Cranyozen/QF_HP_HWJRT/找羊量产初号机资料/贴纸/高壓危險.jpg

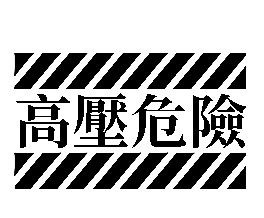
找羊量产初号机资料/贴纸/高壓危險.jpg
