Cranyozen/QF_HP_HWJRT/固件/ESP8266/include/bmp.h

#ifndef _BMP_H_
#define _BMP_H_

const unsigned char circle_shi[] = {
	9, 9, 0x38, 0xFE, 0xFE, 0xFF, 0xFF, 0xFF, 0xFE, 0xFE, 0x38, 0x00, 0x00, 0x00, 0x01, 0x01, 0x01, 0x00,
	0x00, 0x00, /*"E:\Program\通用库\图标库\图标库\实心选择圆.bmp",0*/
				/* (9 X 9 )*/

};

const unsigned char circle_kong[] = {
	9, 9, 0x38, 0xC6, 0x82, 0x01, 0x01, 0x01, 0x82, 0xC6, 0x38, 0x00, 0x00, 0x00, 0x01, 0x01, 0x01, 0x00,
	0x00, 0x00, /*"E:\Program\通用库\图标库\图标库\空心选择圆.bmp",0*/
				/* (9 X 9 )*/

};

const unsigned char number[10][80] = // 20*32
	{
		// 0
		{
			0xFF, 0xFF, 0xFF, 0x07, 0x07, 0x07, 0x07, 0x07, 0x07, 0x07, 0x07, 0x07, 0x07, 0x07, 0x07, 0x07,
			0x07, 0xFF, 0xFF, 0xFF, 0xFF, 0xFF, 0xFF, 0x00, 0x00, 0x00, 0x00, 0x00, 0x00, 0x00, 0x00, 0x00,
			0x00, 0x00, 0x00, 0x00, 0x00, 0xFF, 0xFF, 0xFF, 0xFF, 0xFF, 0xFF, 0x00, 0x00, 0x00, 0x00, 0x00,
			0x00, 0x00, 0x00, 0x00, 0x00, 0x00, 0x00, 0x00, 0x00, 0xFF, 0xFF, 0xFF, 0xFF, 0xFF, 0xFF, 0xE0,
			0xE0, 0xE0, 0xE0, 0xE0, 0xE0, 0xE0, 0xE0, 0xE0, 0xE0, 0xE0, 0xE0, 0xE0, 0xE0, 0xFF, 0xFF, 0xFF, // 0
		},

		// 1
		{
			0x00, 0x00, 0x70, 0x70, 0x38, 0x38, 0x1C, 0x1C, 0x0E, 0x0E, 0xFF, 0xFF, 0xFF, 0x00, 0x00, 0x00,
			0x00, 0x00, 0x00, 0x00, 0x00, 0x00, 0x00, 0x00, 0x00, 0x00, 0x00, 0x00, 0x00, 0x00, 0xFF, 0xFF,
			0xFF, 0x00, 0x00, 0x00, 0x00, 0x00, 0x00, 0x00, 0x00, 0x00, 0x00, 0x00, 0x00, 0x00, 0x00, 0x00,
			0x00, 0x00, 0xFF, 0xFF, 0xFF, 0x00, 0x00, 0x00, 0x00, 0x00, 0x00, 0x00, 0xE0, 0xE0, 0xE0, 0xE0,
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
	0x00, 0x01, 0x02, 0x04, 0x09, 0x12, 0x24, 0x48, 0x90, 0x20, 0x40, 0x80, 0x00, 0x00, 0x00, 0x00,
	0x00, 0x00, 0x00, 0x00, 0x00, 0x00, 0x00, 0x00, 0x00, 0x01, 0x02, 0x04, 0x09, 0x12, 0x24, 0x38, /*"E:\Program\通用库\图标库\图标库\小于16-30.bmp",0*/
																									/* (16 X 30 )*/
};

#endif
