Cranyozen/QF_HP_HWJRT/固件/ESP8266/include/ui.h

#ifndef _ui_H_
#define _ui_H_

#include "User.h"
#include "EC11.h"

typedef enum
{
    show_disable,
    show_set_temp,
    show_now_temp,
    show_set_light,
    show_temp_mode1_time
} ui_show_scr_t;

typedef enum
{
    back,
    sure
} key_value_t;

/**
 * @brief
 *
 * @param 0 启凡科创风格
 * @param 1 找🐏初号机风格
 */
#define compile_style 0 // UI编译风格配置

void ui_key_callb(ec11_task_result_type ec_type, int16_t ec_value);

class UI
{

public:
    void run_task();

    bool page_switch(uint8_t mode);

    void page1_key(ec11_task_result_type ec_type, int16_t ec_value);
    void page2_key(ec11_task_result_type ec_type, int16_t ec_value);
    void page3_key(ec11_task_result_type ec_type, int16_t ec_value);

    bool oled_display_set();

    uint8_t show_temp_mode = show_now_temp;
    uint8_t temp_move_flg = 0; // 温度显示切换标志
    uint8_t temp_mode_flg = 0; // 加热模式切换标志
    uint8_t heat_flg = 0;      // 加热开关切换标志
    bool page_switch_flg = 1;  // 界面切换标志
    int8_t switch_buf = sure;
    bool temp_time_switch_flg = 0;
    bool oled_sleep_flg = 0;

    bool wake_sleep_change_flg = 0;

private:
    void show_temp(int8_t x, int8_t y, int8_t xx, int8_t yy);
    void show_page(short x, short y, uint8_t page);
    void temp_move();
    void temp_mode_move();
    void heat_move();
    void page2_move();
    void page3_switch();
    void blinker_config();
    void write_oled_light();
    void show_curve(int8_t y, int8_t data_y);
    void temp_time_switch();
    void wake_sleep_page();
    void error_temp_fix_page_move();
    void show_warning();
    void page3_push_back();
    void choose_options_move();

    uint8_t set_temp_x = 92;
    uint8 show_warning_flg = 0;

    int8_t miot_option_buf = 0;

    bool blinker_config_flg = 0;
    bool write_oled_flg = 0;
    uint8_t error_temp_fix_page_buf = 0;
    uint8_t error_temp_fix_page_move_buf = 0;

    uint8_t set_var_tmp;
    uint8_t circle_move_buf;
};

extern UI ui;
extern uint8_t show_temp_mode;

#endif
